felixkosmalla/sensor-insole-prototyping/scaled_insole_pdfs/scaled_270mm.pdf

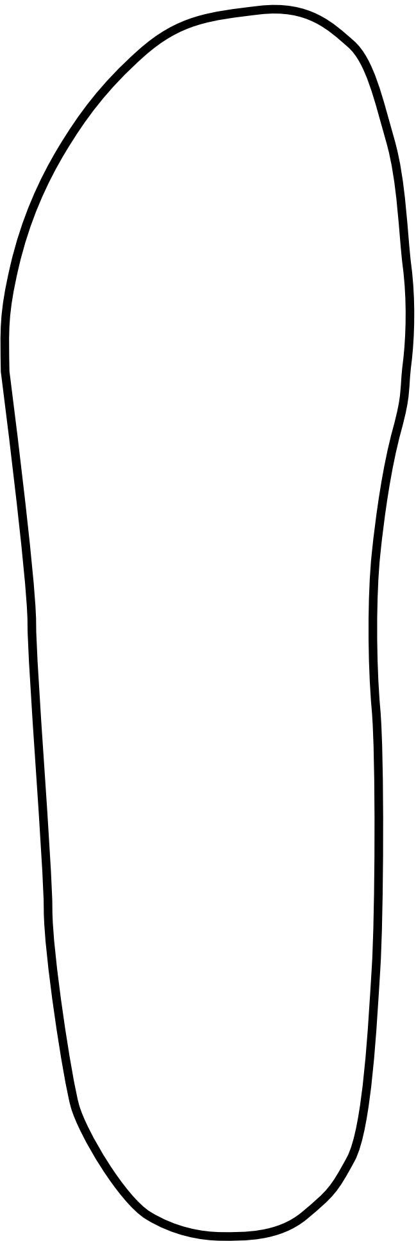
[picture p12: figure]
