felixkosmalla/sensor-insole-prototyping/scaled_insole_pdfs/scaled_275mm.pdf

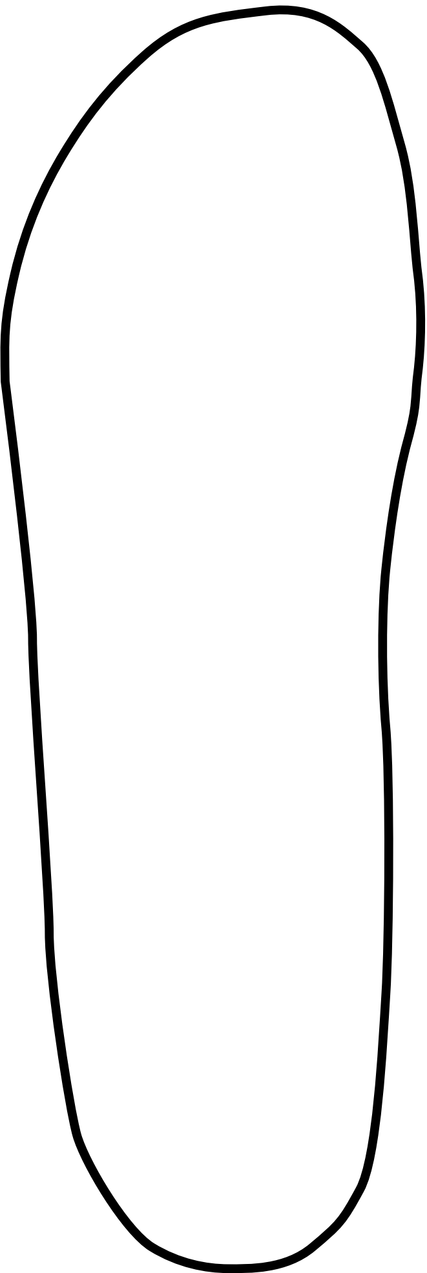
[picture p13: figure]
