felixkosmalla/sensor-insole-prototyping/scaled_insole_pdfs/scaled_280mm.pdf

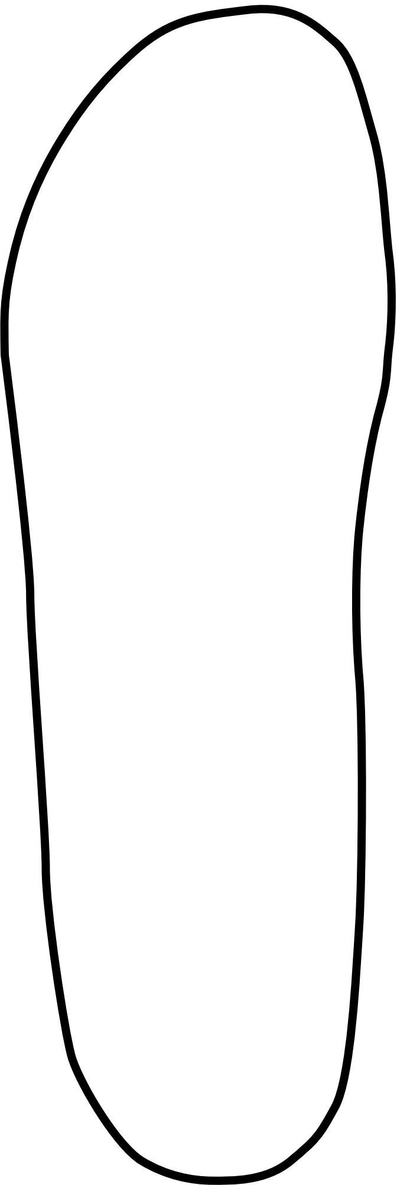
[picture p14: figure]
