felixkosmalla/sensor-insole-prototyping/scaled_insole_pdfs/scaled_285mm.pdf

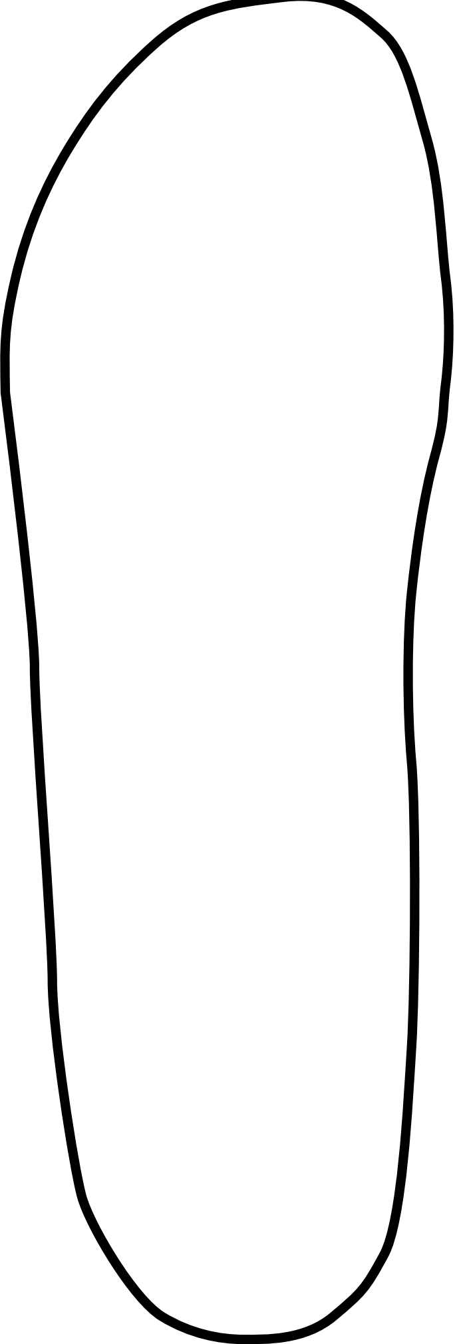
[picture p15: figure]
